FBServiceTech3D/Voron-SKT/Stuff/STL/1.3 - Tap/Hotends/Phaetus Taichi/Mount for Taichi.stl

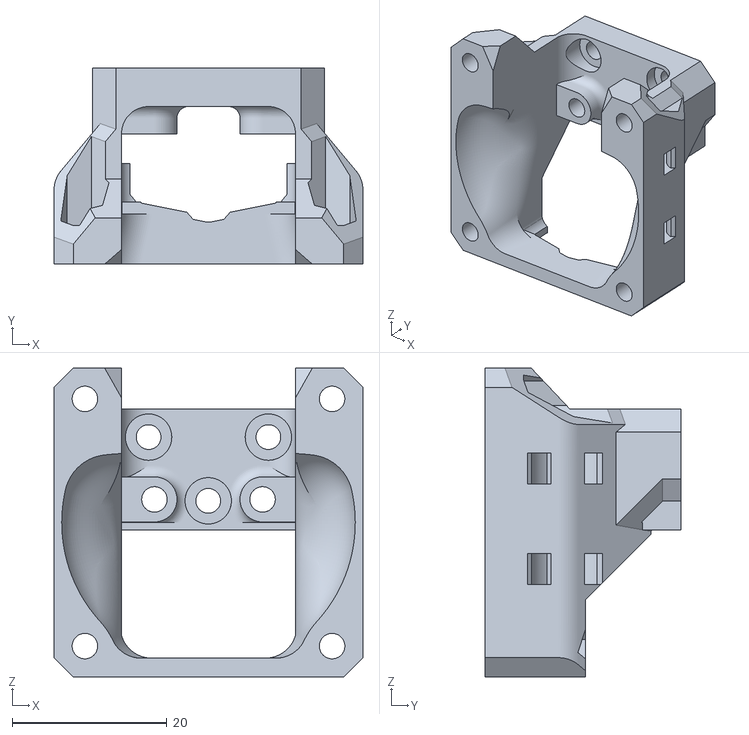
[picture p15: CAD file, 2023-03-19]
Stuff/STL/1.3 - Tap/Hotends/Phaetus Taichi/Mount for Taichi.stl
40.0 x 25.4 x 40.0
