FBServiceTech3D/Voron-SKT/Stuff/STL/1.3 - Tap/Specific fo 2.4/Z-Chain-Horizontal.stl

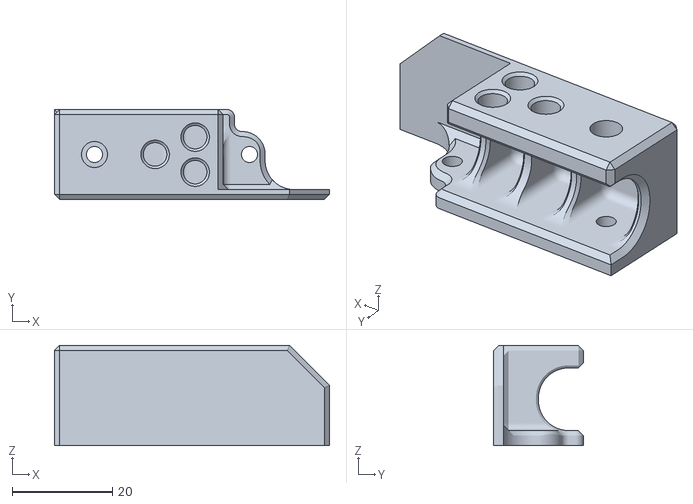
[picture p16: CAD file, 2023-03-19]
Stuff/STL/1.3 - Tap/Specific fo 2.4/Z-Chain-Horizontal.stl
55.0 x 18.0 x 20.0
