FBServiceTech3D/Voron-SKT/Stuff/STL/1.3 - Tap/Specific for Trident/z_stepper_rear_skt-10mm.stl

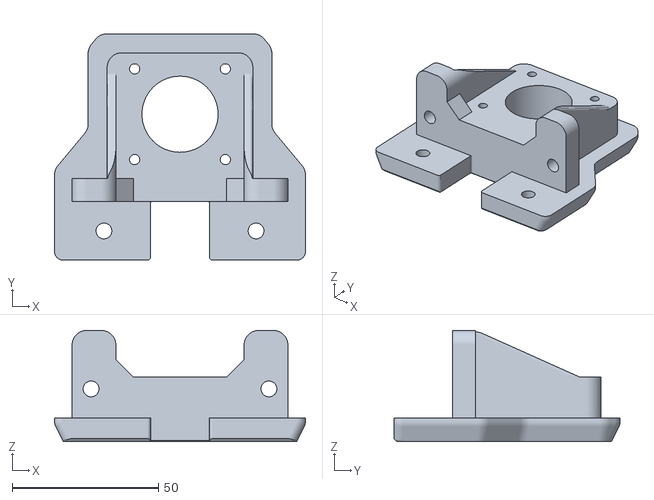
[picture p17: CAD file, 2023-03-19]
Stuff/STL/1.3 - Tap/Specific for Trident/z_stepper_rear_skt-10mm.stl
85.8 x 77.4 x 38.0
