FBServiceTech3D/Voron-SKT/Stuff/STL/1.3 - Tap/Extruders/Mount for Vz-Hextrudort Motor high.stl

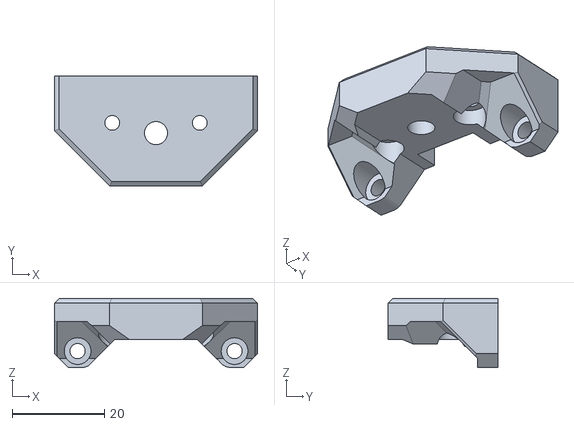
[picture p18: CAD file, 2023-03-19]
Stuff/STL/1.3 - Tap/Extruders/Mount for Vz-Hextrudort Motor high.stl
44.1 x 23.9 x 15.0
