FBServiceTech3D/Voron-SKT/Stuff/STL/1.3 - Tap/Mgn12 Version/Carriage/Top.stl

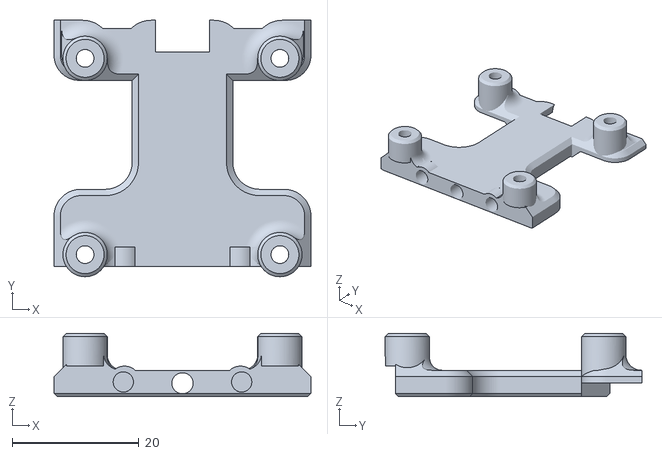
[picture p19: CAD file, 2023-06-22]
Stuff/STL/1.3 - Tap/Mgn12 Version/Carriage/Top.stl
40.6 x 40.5 x 9.96
