FBServiceTech3D/Voron-SKT/Stuff/STL/1.3 - Tap/Mgn12 Version/Tap System/Distanziale OctoTap.stl

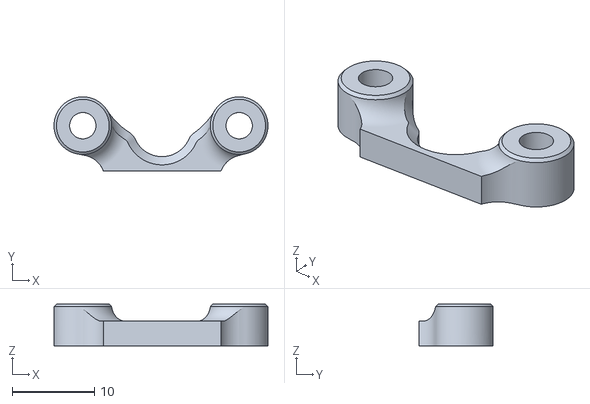
[picture p20: CAD file, 2023-03-19]
Stuff/STL/1.3 - Tap/Mgn12 Version/Tap System/Distanziale OctoTap.stl
26.0 x 9.02 x 5.08
