FBServiceTech3D/Voron-SKT/Stuff/STL/FacePlates/Skull.stl

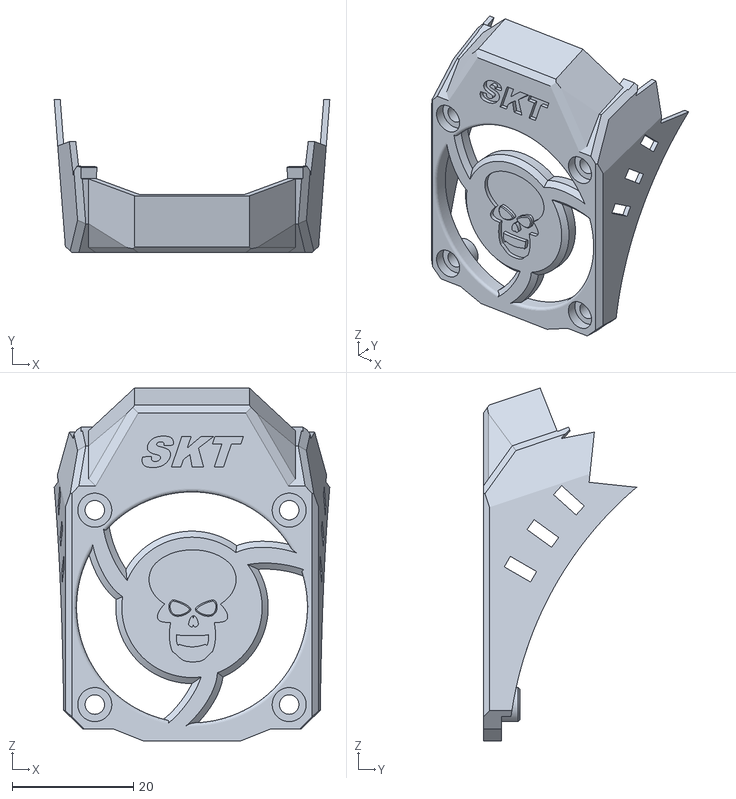
[picture p21: CAD file, 2023-03-19]
Stuff/STL/FacePlates/Skull.stl
45.4 x 25.2 x 58.1
