FBServiceTech3D/Voron-SKT/Stuff/STL/1.3 - Tap/Extruders/Mount for Sherpa Mini.stl

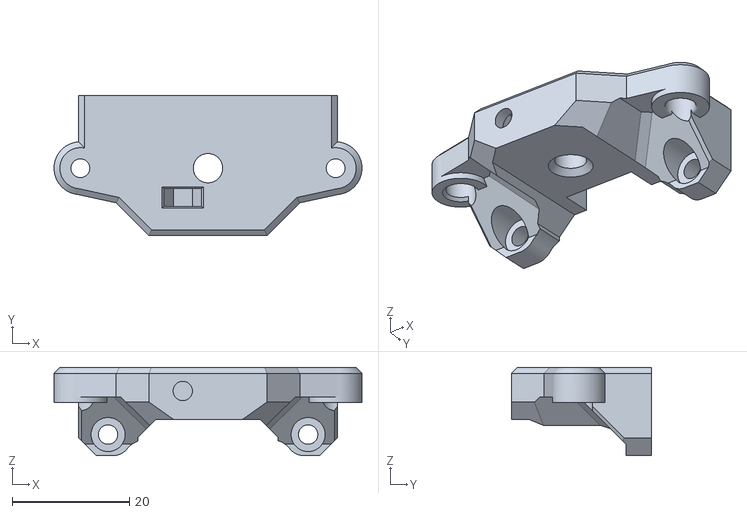
[picture p22: CAD file, 2023-03-19]
Stuff/STL/1.3 - Tap/Extruders/Mount for Sherpa Mini.stl
52.5 x 23.9 x 15.0
