FBServiceTech3D/Voron-SKT/Stuff/STL/1.3 - Tap/Mgn12 Version/Carriage/Front.stl

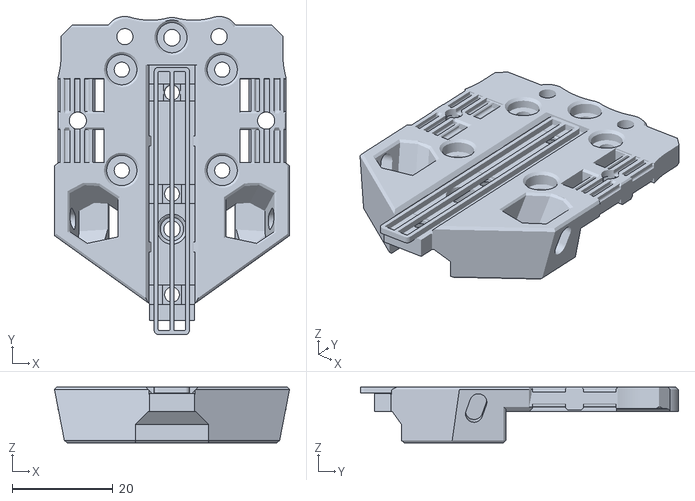
[picture p23: CAD file, 2023-06-22]
Stuff/STL/1.3 - Tap/Mgn12 Version/Carriage/Front.stl
46.6 x 63.1 x 11.1
