FBServiceTech3D/Voron-SKT/Stuff/STL/1.3 - Tap/Mgn12 Version/Tap System/Center-right.stl

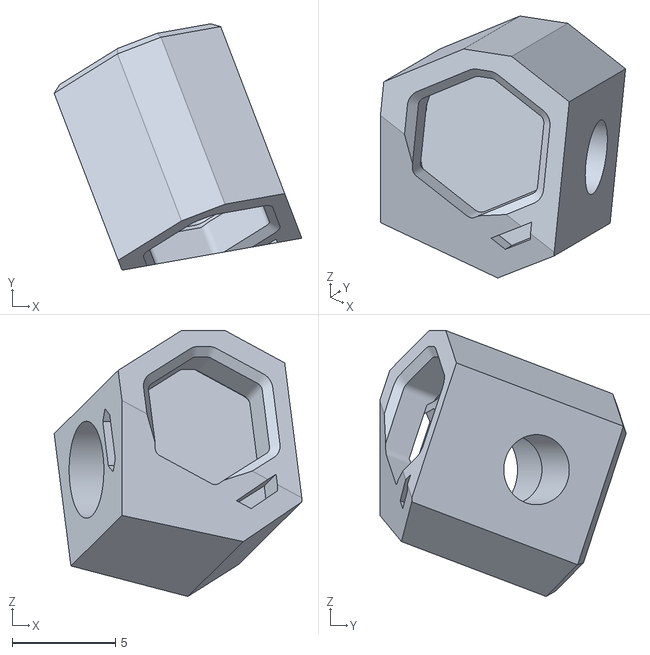
[picture p24: CAD file, 2023-03-19]
Stuff/STL/1.3 - Tap/Mgn12 Version/Tap System/Center-right.stl
12.0 x 12.0 x 12.9
