FBServiceTech3D/Voron-SKT/Stuff/STL/FacePlates/Skull No Eyes.stl

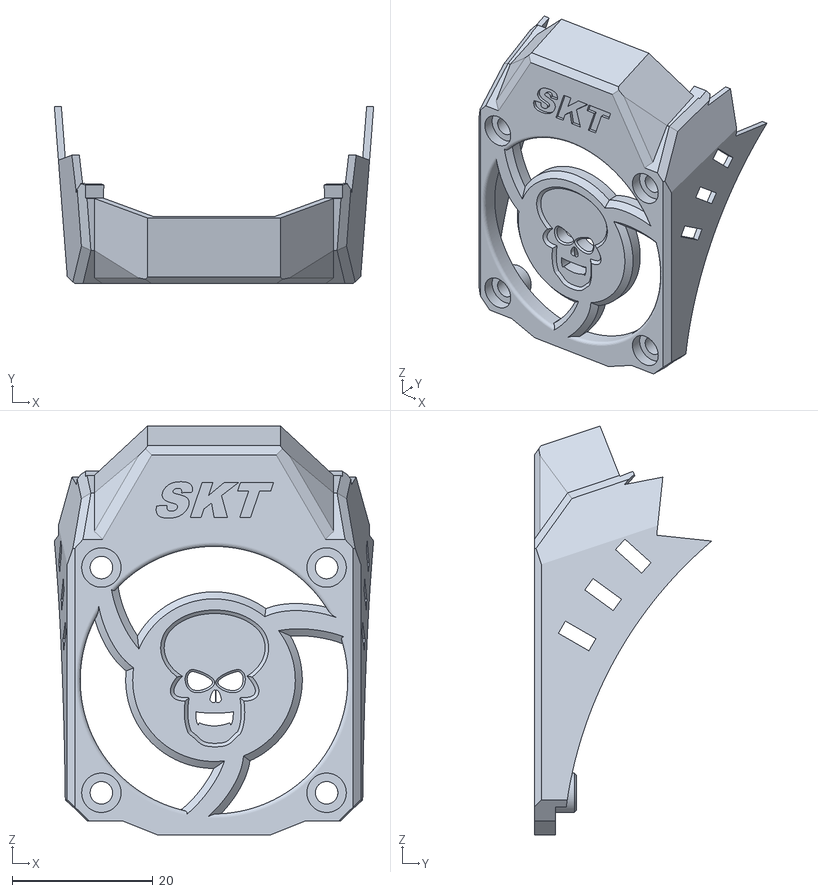
[picture p25: CAD file, 2023-03-19]
Stuff/STL/FacePlates/Skull No Eyes.stl
45.4 x 25.2 x 58.1
