FBServiceTech3D/Voron-SKT/Stuff/STL/1.3 - Tap/Mgn12 Version/Carriage/Rear.stl

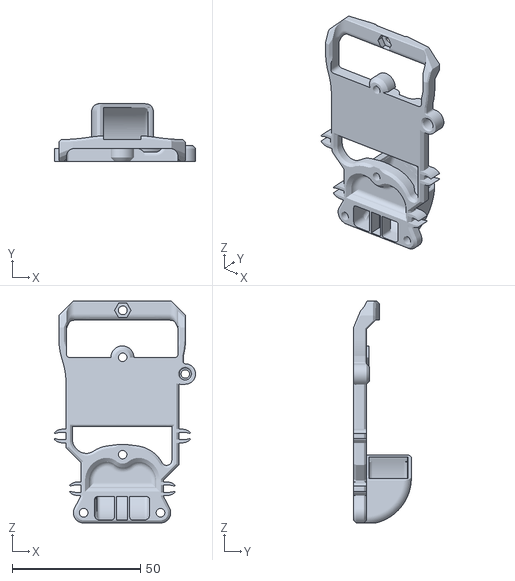
[picture p27: CAD file, 2023-03-19]
Stuff/STL/1.3 - Tap/Mgn12 Version/Carriage/Rear.stl
55.1 x 22.5 x 86.7
