FBServiceTech3D/Voron-SKT/Stuff/STL/FacePlates/SKT.stl

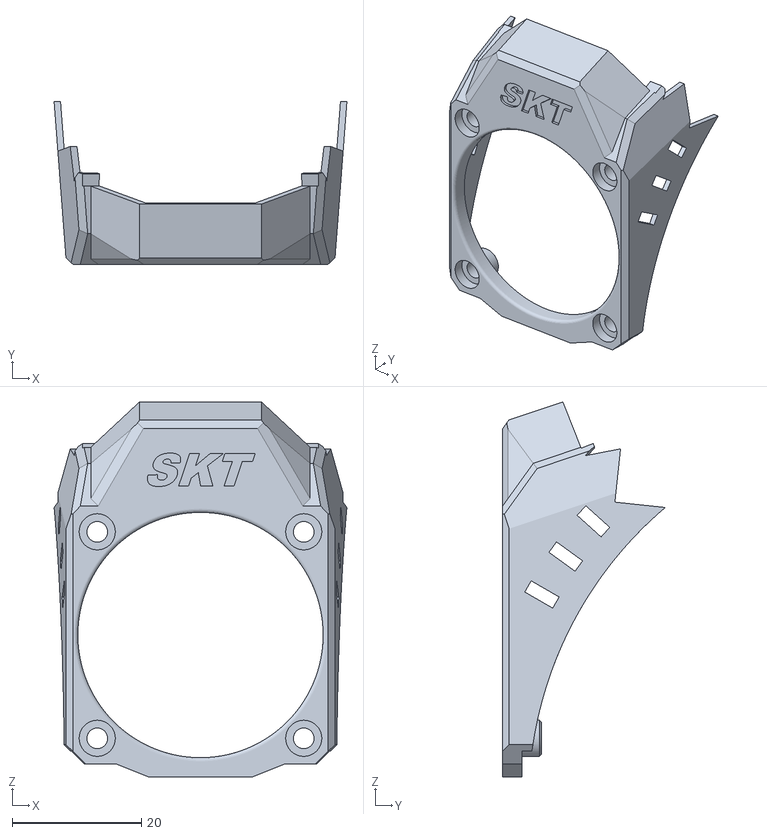
[picture p28: CAD file, 2023-03-19]
Stuff/STL/FacePlates/SKT.stl
45.4 x 25.2 x 58.1
