FBServiceTech3D/Voron-SKT/Stuff/STL/1.3 - Tap/Extruders/Mount for Orbiter 1.5.stl

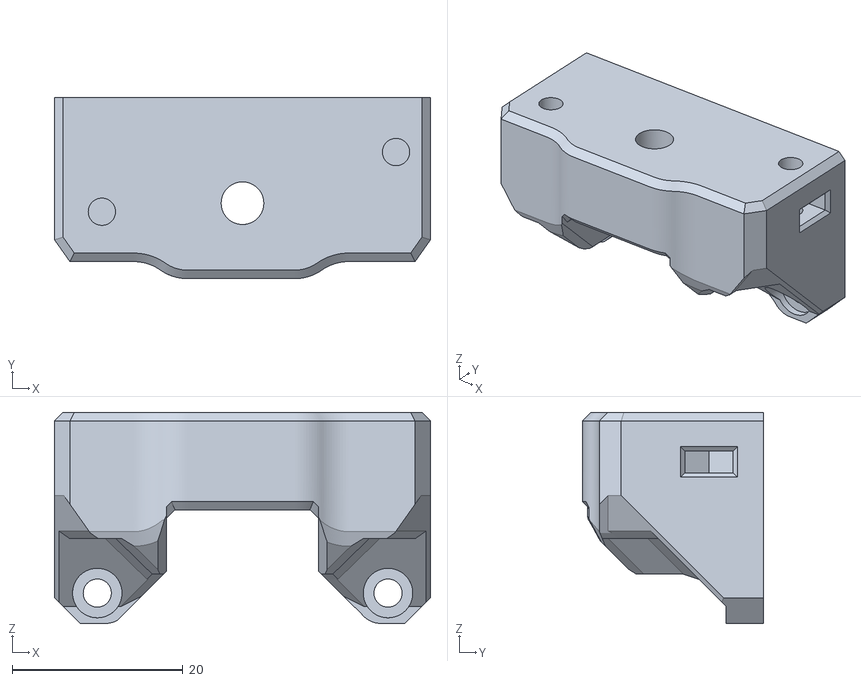
[picture p29: CAD file, 2023-03-19]
Stuff/STL/1.3 - Tap/Extruders/Mount for Orbiter 1.5.stl
44.1 x 21.3 x 24.8
