FBServiceTech3D/Voron-SKT/Stuff/STL/1.3 - Tap/Mgn12 Version/Carriage/Bottom.stl

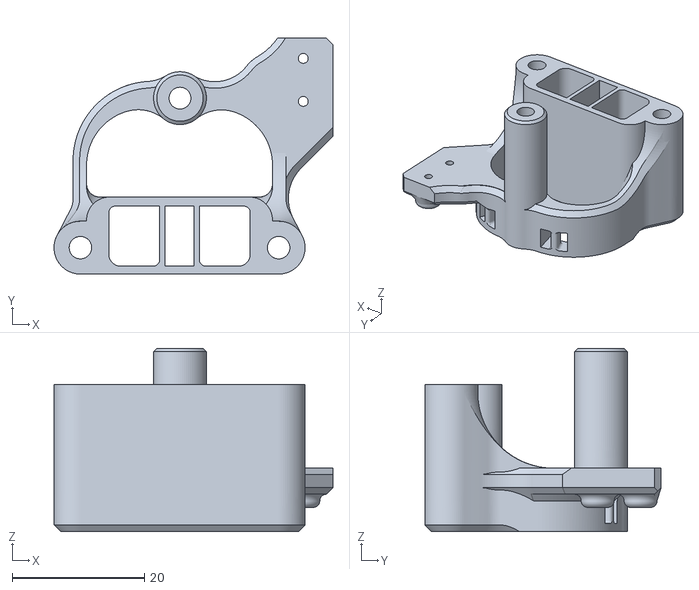
[picture p30: CAD file, 2023-03-19]
Stuff/STL/1.3 - Tap/Mgn12 Version/Carriage/Bottom.stl
42.2 x 35.7 x 27.7
