FBServiceTech3D/Voron-SKT/Stuff/STL/FacePlates/SKT - fan 4010 without holes.stl

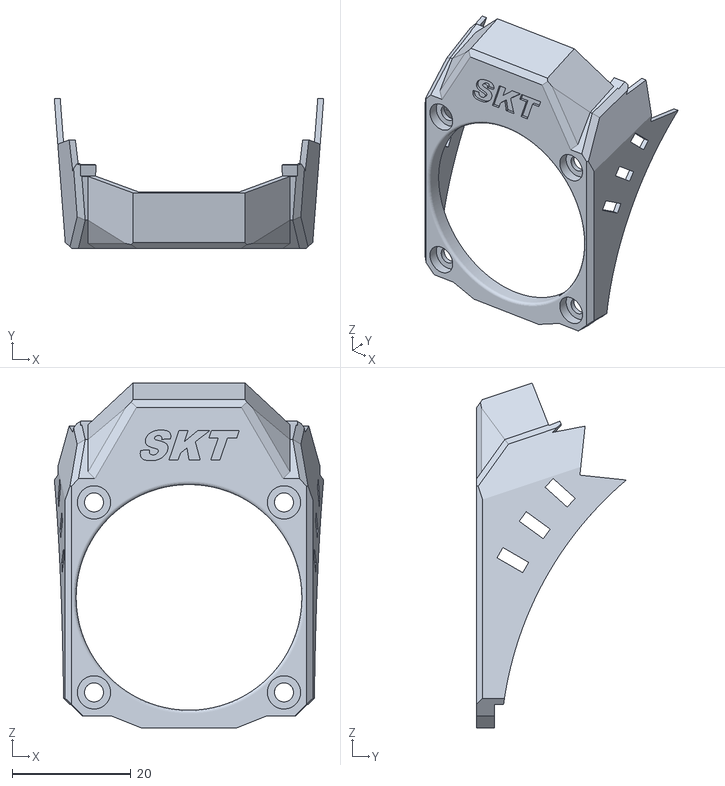
[picture p31: CAD file, 2023-03-19]
Stuff/STL/FacePlates/SKT - fan 4010 without holes.stl
45.4 x 25.2 x 58.1
