FBServiceTech3D/Voron-SKT/Stuff/STL/1.3 - Tap/Extruders/Mount for Lgx Lite.stl

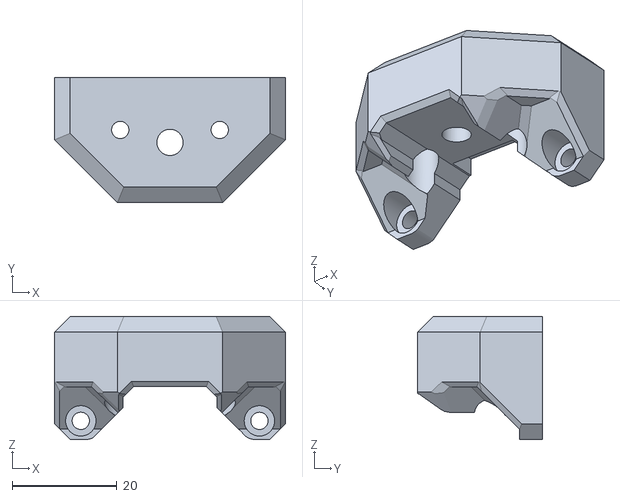
[picture p32: CAD file, 2023-03-19]
Stuff/STL/1.3 - Tap/Extruders/Mount for Lgx Lite.stl
44.1 x 23.9 x 23.5
